kirilDen/Mini_FPV_RC_CAR_WiFi/Stl_Files/RightSpindle.stl

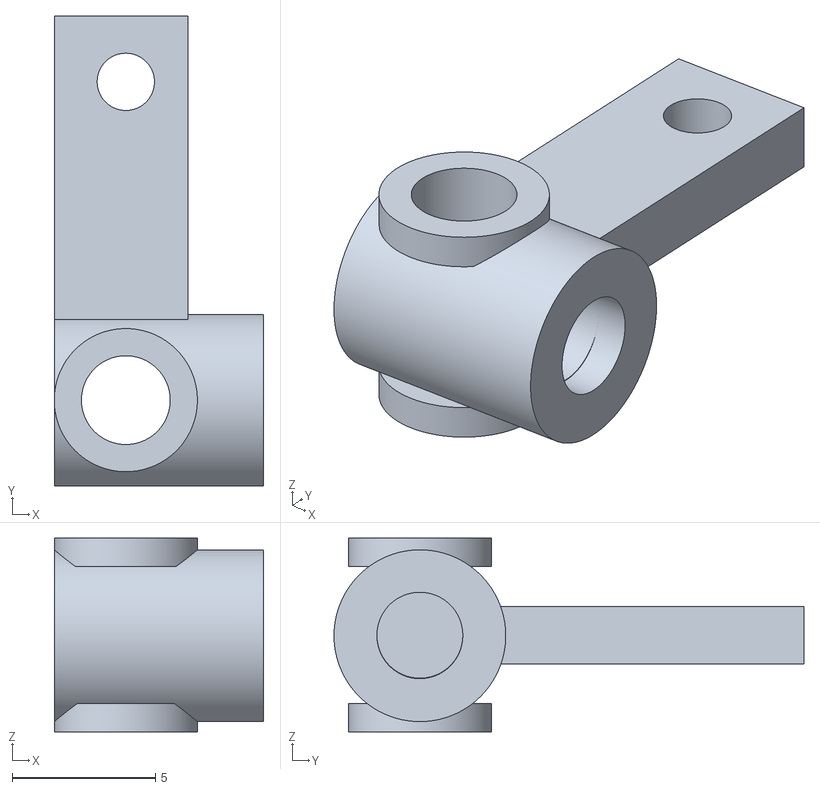
[picture p15: CAD file, 2026-08-16]
Stl_Files/RightSpindle.stl
7.32 x 16.4 x 6.77
