kirilDen/Mini_FPV_RC_CAR_WiFi/Stl_Files/Chassis_stl.stl

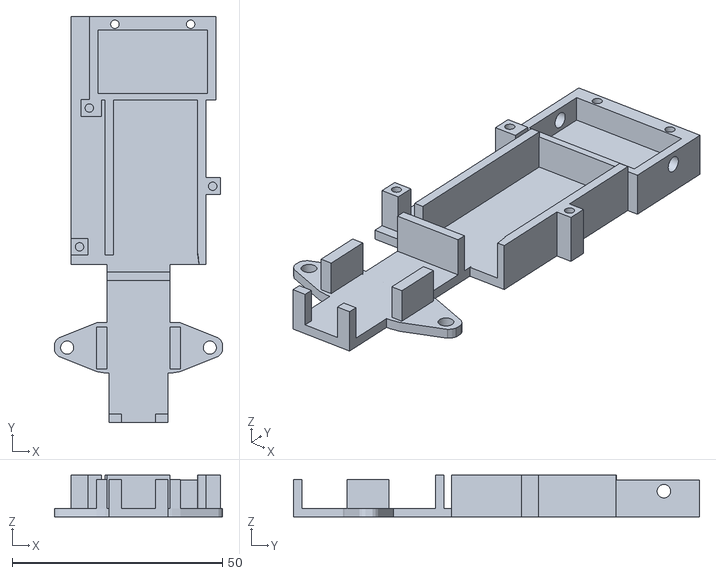
[picture p16: CAD file, 2026-08-16]
Stl_Files/Chassis_stl.stl
40.0 x 96.5 x 9.90
