kirilDen/Mini_FPV_RC_CAR_WiFi/Stl_Files/DriverMotor_Mount.stl

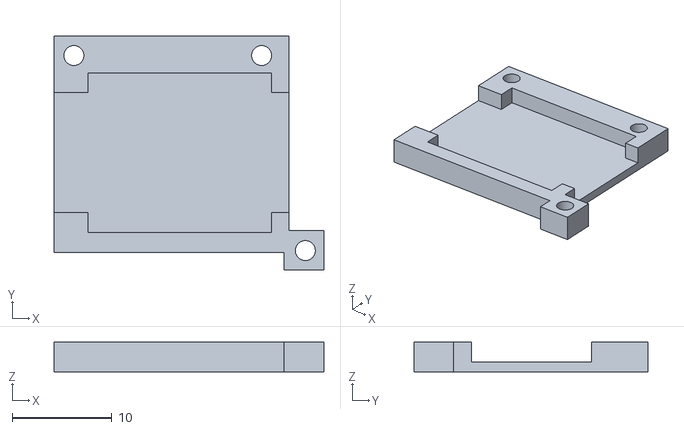
[picture p17: CAD file, 2026-08-16]
Stl_Files/DriverMotor_Mount.stl
27.1 x 23.5 x 3.00
