kirilDen/Mini_FPV_RC_CAR_WiFi/Stl_Files/MotorGear.stl

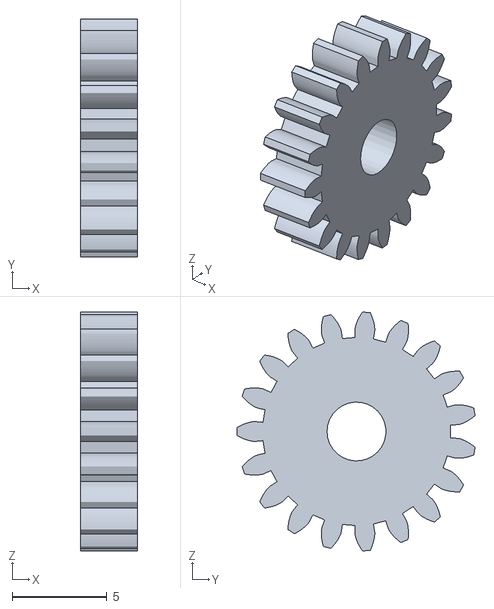
[picture p18: CAD file, 2026-08-13]
Stl_Files/MotorGear.stl
3.00 x 12.5 x 12.6
