kirilDen/Mini_FPV_RC_CAR_WiFi/Stl_Files/steeringHigh.stl

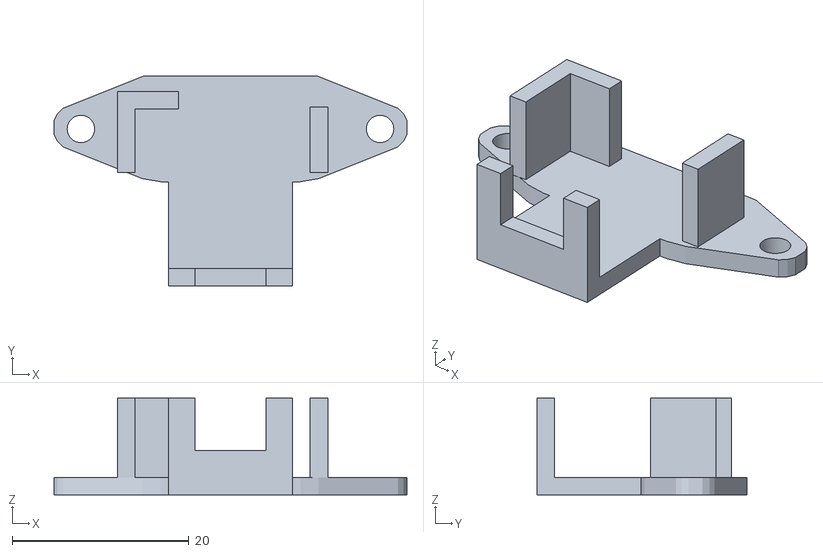
[picture p19: CAD file, 2026-08-13]
Stl_Files/steeringHigh.stl
40.0 x 23.8 x 11.0
