kirilDen/Mini_FPV_RC_CAR_WiFi/Stl_Files/UpperBack.stl

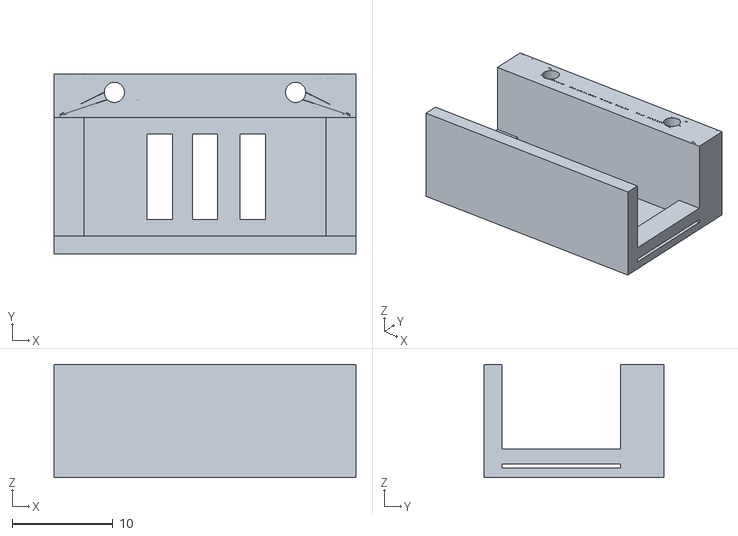
[picture p20: CAD file, 2026-08-13]
Stl_Files/UpperBack.stl
30.0 x 17.9 x 11.2
