kirilDen/Mini_FPV_RC_CAR_WiFi/Stl_Files/Steering Arm.stl

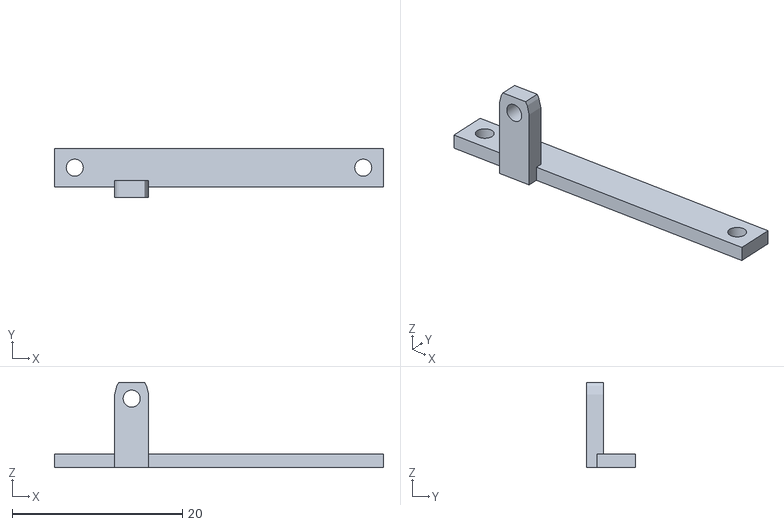
[picture p21: CAD file, 2026-08-12]
Stl_Files/Steering Arm.stl
38.7 x 5.75 x 10.00
